Bhumipat001/FIBO-Academy-2025/Desktop Friend Robot/Raspberry Pi 4/screen/sleep.gif

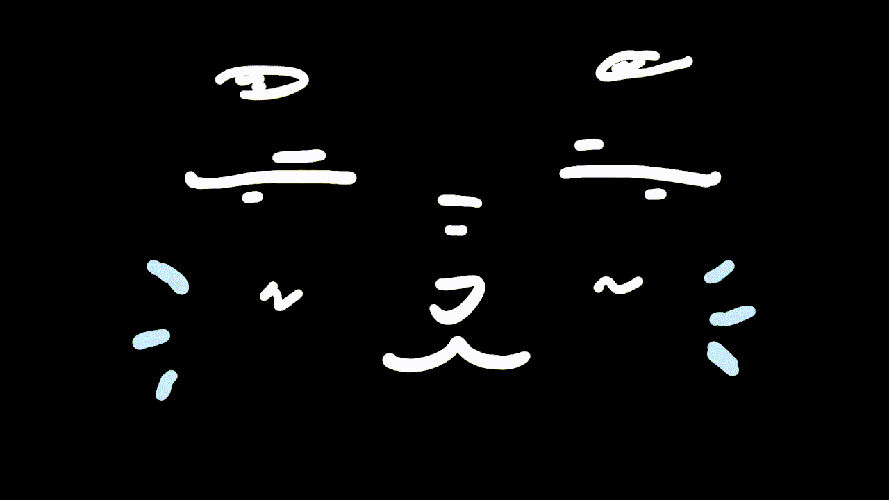
Desktop Friend Robot/Raspberry Pi 4/screen/sleep.gif
