Bhumipat001/FIBO-Academy-2025/CAD/STL/Head/Head Diff.STL

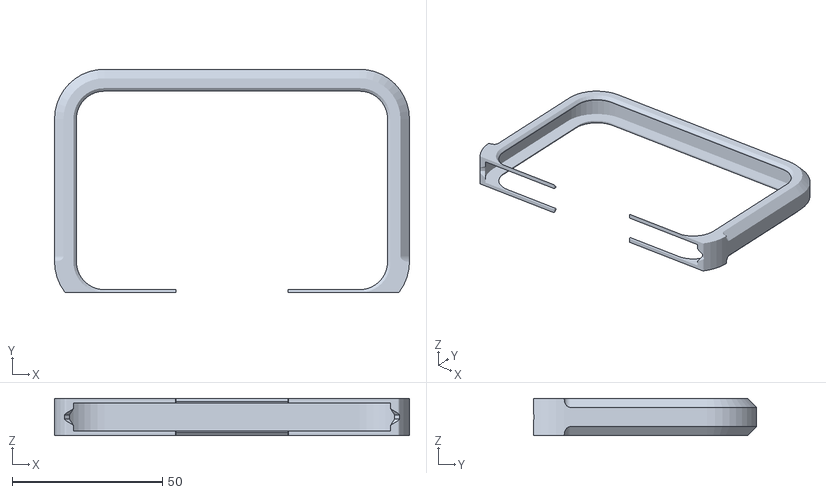
[picture p30: CAD file, 2025-11-03]
CAD/STL/Head/Head Diff.STL
118.1 x 74.4 x 12.4
