Bhumipat001/FIBO-Academy-2025/CAD/STL/Base and Leg/Speaker Holder.STL

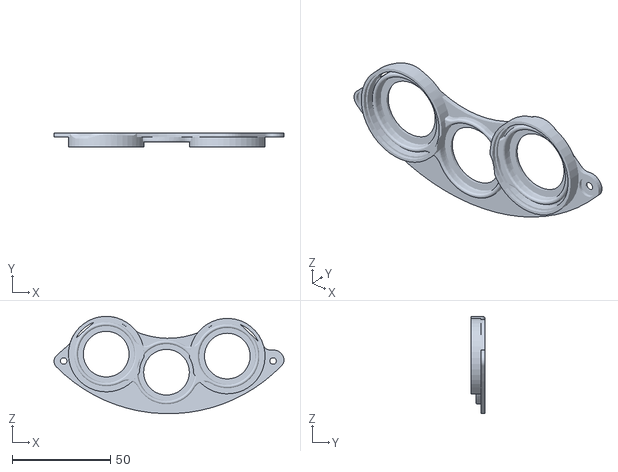
[picture p31: CAD file, 2025-11-03]
CAD/STL/Base and Leg/Speaker Holder.STL
117.0 x 6.95 x 49.5
