Bhumipat001/FIBO-Academy-2025/CAD/STL/Body/Body Left Cover.STL

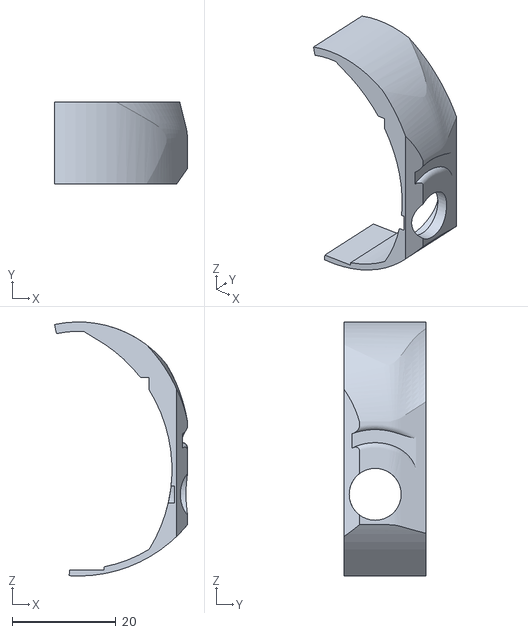
[picture p32: CAD file, 2025-11-03]
CAD/STL/Body/Body Left Cover.STL
25.6 x 15.8 x 48.9
