Bhumipat001/FIBO-Academy-2025/CAD/STL/Base and Leg/Base Connector Gear.STL

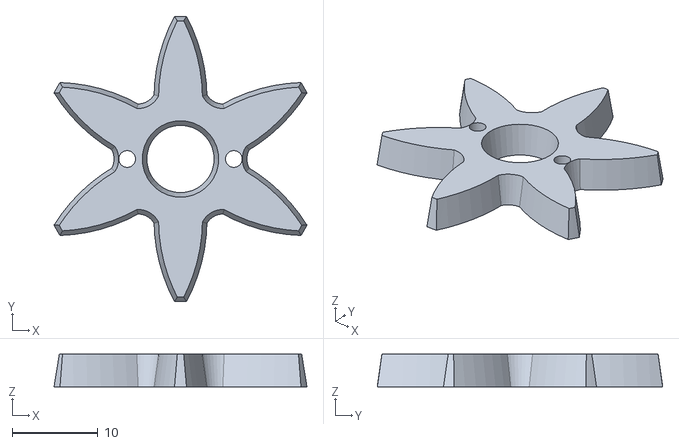
[picture p33: CAD file, 2025-11-03]
CAD/STL/Base and Leg/Base Connector Gear.STL
29.5 x 33.3 x 3.80
