Bhumipat001/FIBO-Academy-2025/CAD/STL/Body/Gear Right.STL

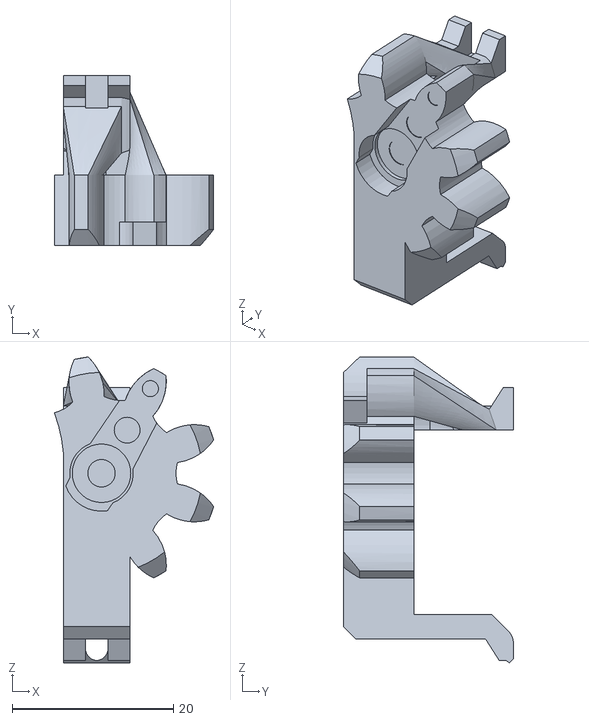
[picture p34: CAD file, 2025-11-03]
CAD/STL/Body/Gear Right.STL
19.7 x 21.1 x 37.9
