Bhumipat001/FIBO-Academy-2025/CAD/STL/Head/Left Ear.STL

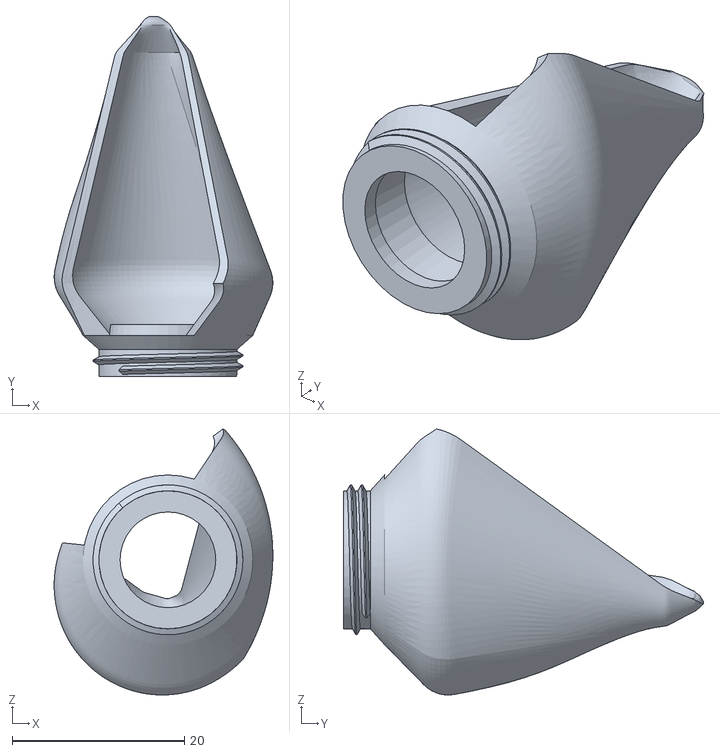
[picture p35: CAD file, 2025-11-03]
CAD/STL/Head/Left Ear.STL
25.4 x 41.8 x 30.9
