Bhumipat001/FIBO-Academy-2025/CAD/STL/Base and Leg/Base Connector.STL

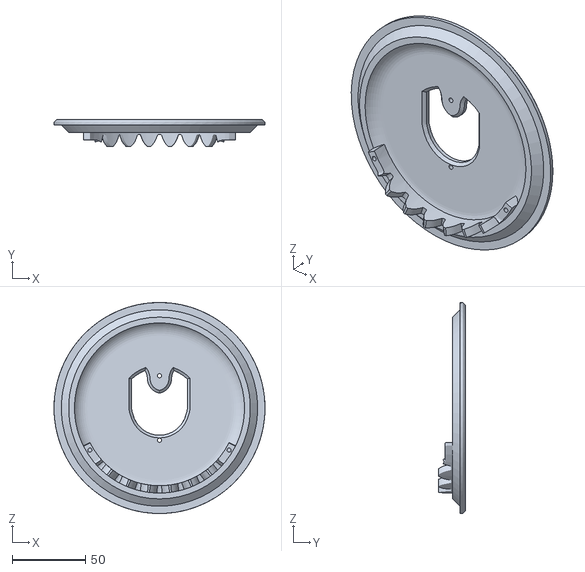
[picture p36: CAD file, 2025-11-03]
CAD/STL/Base and Leg/Base Connector.STL
144.0 x 18.8 x 144.0
