Bhumipat001/FIBO-Academy-2025/CAD/STL/Body/Body L1.STL

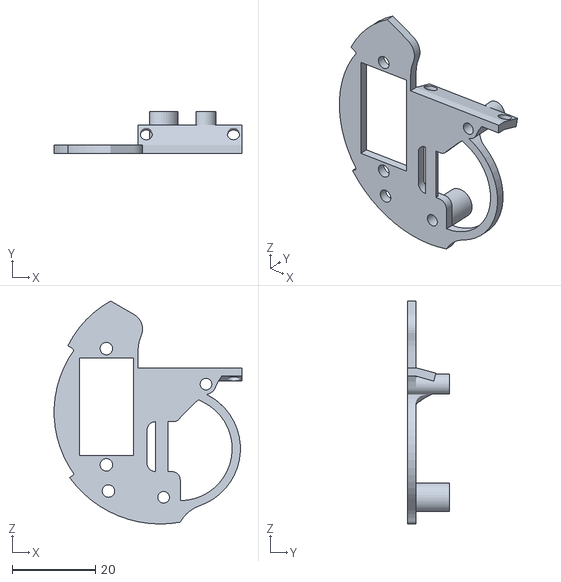
[picture p37: CAD file, 2025-11-03]
CAD/STL/Body/Body L1.STL
45.2 x 10.1 x 53.7
