Bhumipat001/FIBO-Academy-2025/CAD/STL/Base and Leg/Leg.STL

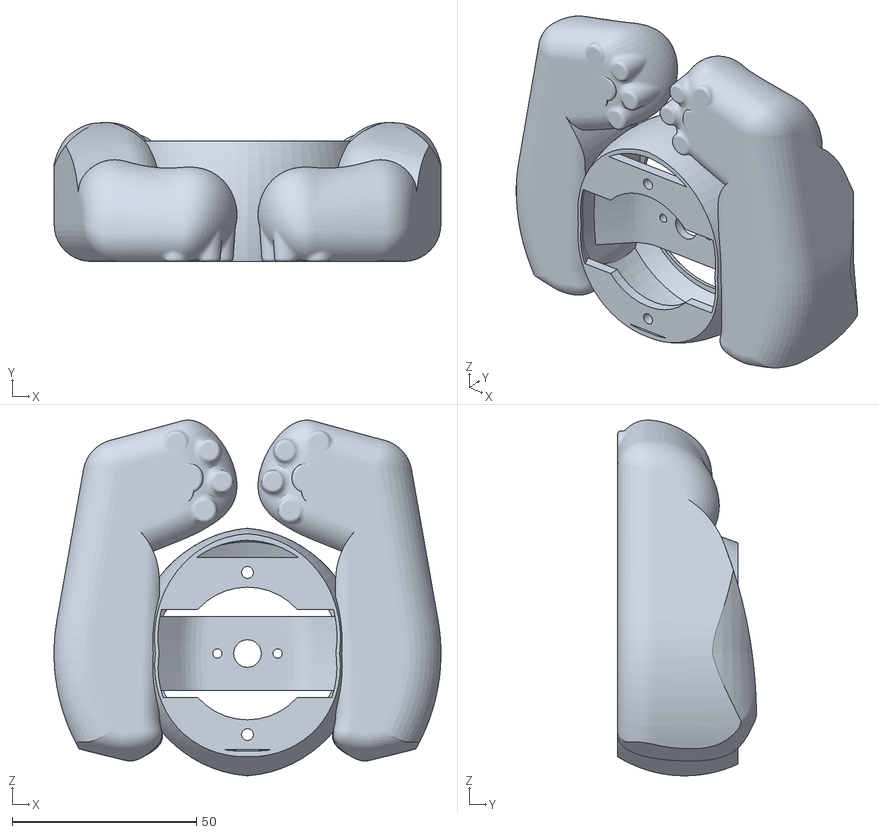
[picture p38: CAD file, 2025-11-03]
CAD/STL/Base and Leg/Leg.STL
105.0 x 37.7 x 96.5
