Bhumipat001/FIBO-Academy-2025/CAD/STL/Body/Body.STL

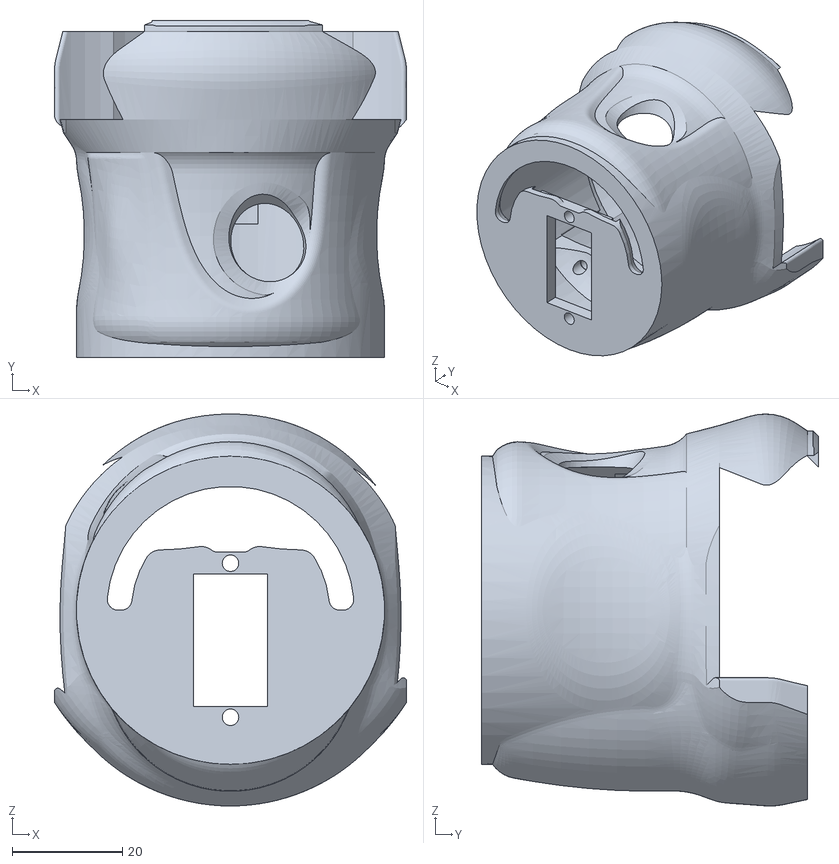
[picture p39: CAD file, 2025-11-03]
CAD/STL/Body/Body.STL
64.0 x 61.2 x 71.2
