Bhumipat001/FIBO-Academy-2025/CAD/STL/Head/Head Shell.STL

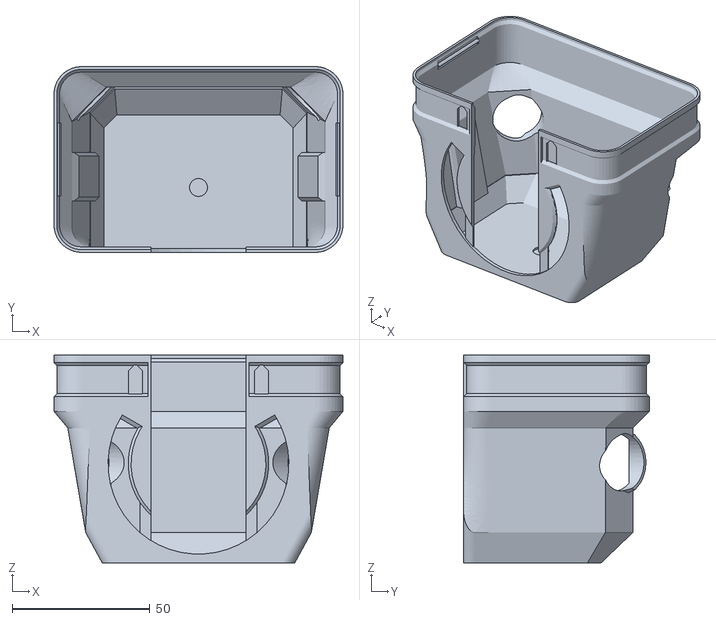
[picture p40: CAD file, 2025-11-03]
CAD/STL/Head/Head Shell.STL
105.0 x 67.5 x 75.4
