Bhumipat001/FIBO-Academy-2025/CAD/STL/Head/Head Structure.STL

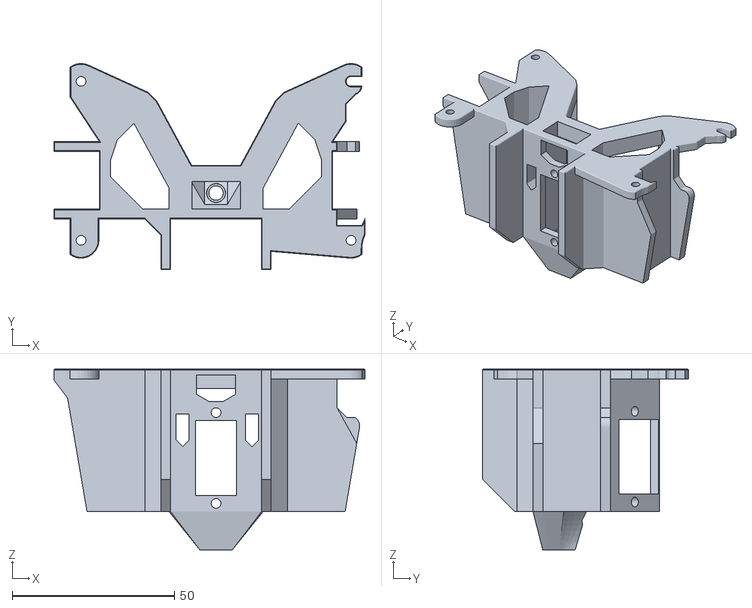
[picture p41: CAD file, 2025-11-03]
CAD/STL/Head/Head Structure.STL
96.0 x 63.5 x 55.8
