Bhumipat001/FIBO-Academy-2025/img/Touching Test.png

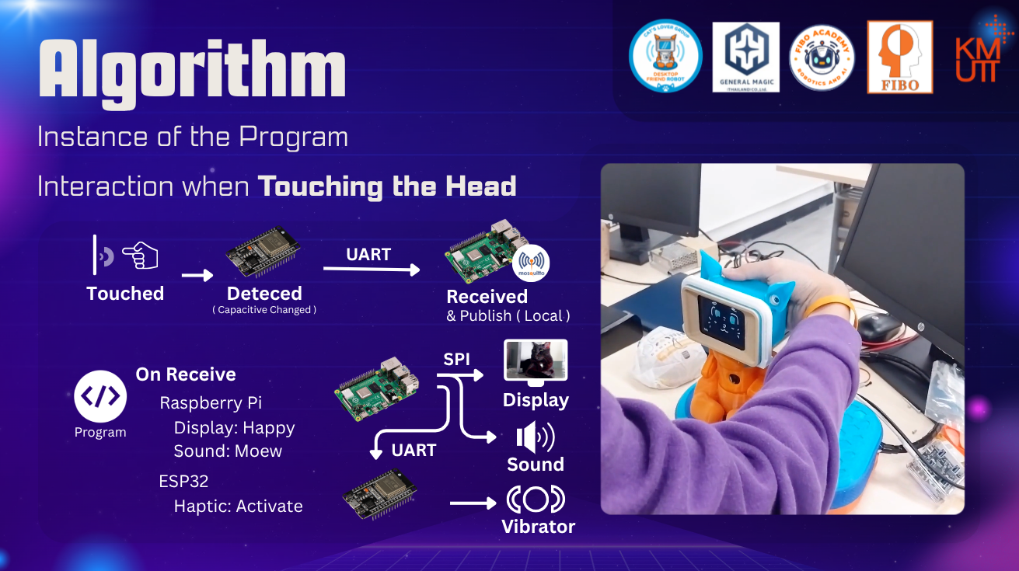
img/Touching Test.png
